abzman/RFID-entry-system/printer_test/printer_test.ino

//Printer Pins
const int dataPins[] = {41,42,43,44,45,46,47,48};
const int strobePin = 39;//active low
//const int lineFeedPin = 40;//active low
//const int errorPin = 41;
//const int resetPin = 42;
//const int ackPin = 43;
const int busyPin = 40;//active low
//const int paperOutPin = 45;
//const int selPin = 46;//high if printer is on

//End Printer Pins

char buffer = 0x00;

void setup() {
  //Printer I/O Setup
  for (int i = 0; i < sizeof(dataPins) / sizeof(dataPins[0]); ++i)
    pinMode(dataPins[i], OUTPUT);
  pinMode(strobePin, OUTPUT);
  pinMode(busyPin, INPUT);     
  //pinMode(ackPin, INPUT);
  
  digitalWrite(strobePin, HIGH);
 //End Printer I/O Setup
 
 //Setup init, lf, sel
 //init is ??
 //lf is high
 //sel is low
 
 //Use Serial input to stream to the printer for testing
 Serial.begin(9600);
}

void loop() {
  if (Serial.available() > 0) {
    printer(Serial.read());
  }
}
void printer(char buffer)
{
	//Write out our buffer
	for (int j = 0; j < sizeof(dataPins) / sizeof(dataPins[0]); ++j)
		digitalWrite(dataPins[j], (buffer & (1 << j)));
	//buffer = 0x00;
    
	//Block and wait for the printer to be ready
	while (digitalRead(busyPin));
    
	//Tell the printer to write out the data
	digitalWrite(strobePin, LOW);
	delay(10);
	digitalWrite(strobePin, HIGH);
    
	//Reset the data lines
	for (int j = 0; j < sizeof(dataPins) / sizeof(dataPins[0]); ++j) 
		digitalWrite(dataPins[j], LOW);
}
